MrBroccoliJP/MementoFrame/mementoframe/updater.py

#!/usr/bin/env python3
# MementoFrame - Raspberry Pi Smart Photo Frame
# Updater / installer helper

from __future__ import annotations

import argparse
import hashlib
import json
import runpy
import os
import re
import shutil
import stat
import subprocess
import sys
import tempfile
import threading
import time
import urllib.request
import zipfile
from datetime import datetime
from contextlib import contextmanager
from pathlib import Path
from typing import Any

UPDATER_BUILD = "2026-10-06-install-only-overlay-v3"

PROJECT_ROOT = Path(__file__).resolve().parent
CONFIG_FILE = PROJECT_ROOT / "config.json"
RUNTIME_DIR = PROJECT_ROOT / "runtime"
STATE_FILE = RUNTIME_DIR / "update_state.json"
STATE_LOCK_FILE = RUNTIME_DIR / "update_state.lock"
UPDATER_LOCK_FILE = RUNTIME_DIR / "updater.lock"
DOWNLOAD_DIR = RUNTIME_DIR / "update_downloads"
BACKUP_ROOT = PROJECT_ROOT.parent / "mementoframe_backups"
BACKUP_RETENTION_COUNT = 3
DEFAULT_UPDATE_TIME = "07:00"
DEFAULT_PRESERVE = ["config.json", ".env", "resources/userdata", "runtime"]
DEFAULT_SERVICES = [
    "mementoframe-config.service",
    "mementoframe-display.service",
    "mementoframe-network.service",
    "mementoframe-kiosk.service",
]
SERVICE_TEMPLATE_UNITS = [
    "mementoframe-config.service",
    "mementoframe-display.service",
    "mementoframe-network.service",
    "mementoframe-updater.service",
]
REFRESH_FROM_RELEASE_AFTER_RESTORE = ["repair_services.sh"]

REQUIRED_SYSTEMD_UNITS = [
    "mementoframe-config.service",
    "mementoframe-display.service",
    "mementoframe-network.service",
    "mementoframe-kiosk.service",
    "mementoframe-updater.service",
    "mementoframe-updater.timer",
]
REPAIR_HELPER = PROJECT_ROOT / "repair_services.sh"

HEALTH_URLS = ["http://127.0.0.1:5000/health", "http://127.0.0.1:5001/health"]
HEALTH_CHECK_ATTEMPTS = 3
HEALTH_CHECK_SECONDS = 90
HEALTH_POLL_SECONDS = 3
APP_SUBDIR = "mementoframe"

_LOCAL_STATE_LOCK = threading.RLock()

EXCLUDE_DURING_COPY = {
    ".git",
    "venv",
    "__pycache__",
    ".pytest_cache",
    "node_modules",
    "runtime",
}
SPECIAL_FILE_CLEANUP_SKIP = {
    ".git",
    "venv",
    "node_modules",
    "resources/userdata",
    "runtime",
}


def now_ts() -> int:
    return int(time.time())


def system_boot_id() -> str | None:
    """Return the Linux boot ID, which changes exactly once per reboot."""
    try:
        value = Path("/proc/sys/kernel/random/boot_id").read_text(encoding="utf-8").strip()
        return value or None
    except Exception:
        return None


def system_boot_time() -> float | None:
    """Return the Linux system boot timestamp when available."""
    try:
        for line in Path("/proc/stat").read_text(encoding="utf-8").splitlines():
            if line.startswith("btime "):
                return float(line.split()[1])
    except Exception:
        return None
    return None


def boot_changed_since_update(state: dict[str, Any], *, rollback: bool = False) -> bool:
    """Prove that the system rebooted after applying an update or rollback."""
    if rollback:
        saved_boot_id = state.get("rollback_applied_boot_id") or state.get("rollback_reboot_requested_boot_id")
        marker = state.get("rollback_reboot_requested_at") or state.get("rollback_at") or state.get("updated_at")
    else:
        saved_boot_id = state.get("update_applied_boot_id") or state.get("reboot_requested_boot_id")
        marker = state.get("reboot_requested_at") or state.get("updated_at")

    current_boot_id = system_boot_id()
    if saved_boot_id and current_boot_id:
        return saved_boot_id != current_boot_id

    boot_time = system_boot_time()
    try:
        return bool(boot_time and marker and boot_time >= float(marker))
    except (TypeError, ValueError):
        return False


@contextmanager
def interprocess_file_lock(path: Path, *, blocking: bool = True):
    """Hold a small cross-process lock file on Linux and Windows."""
    path.parent.mkdir(parents=True, exist_ok=True)
    handle = path.open("a+b")
    acquired = False
    platform_lock = None
    try:
        if os.name == "nt":
            import msvcrt

            handle.seek(0, os.SEEK_END)
            if handle.tell() == 0:
                handle.write(b"\0")
                handle.flush()
            handle.seek(0)
            mode = msvcrt.LK_LOCK if blocking else msvcrt.LK_NBLCK
            try:
                msvcrt.locking(handle.fileno(), mode, 1)
                acquired = True
                platform_lock = msvcrt
            except OSError:
                acquired = False
        else:
            import fcntl

            flags = fcntl.LOCK_EX | (0 if blocking else fcntl.LOCK_NB)
            try:
                fcntl.flock(handle.fileno(), flags)
                acquired = True
                platform_lock = fcntl
            except BlockingIOError:
                acquired = False
        yield acquired
    finally:
        if acquired and platform_lock is not None:
            try:
                if os.name == "nt":
                    handle.seek(0)
                    platform_lock.locking(handle.fileno(), platform_lock.LK_UNLCK, 1)
                else:
                    platform_lock.flock(handle.fileno(), platform_lock.LOCK_UN)
            except OSError:
                pass
        handle.close()


@contextmanager
def state_file_lock():
    """Serialize update-state read/modify/write operations across services."""
    with _LOCAL_STATE_LOCK:
        with interprocess_file_lock(STATE_LOCK_FILE) as acquired:
            if not acquired:
                raise RuntimeError("Could not lock update state")
            yield


def atomic_write_json(path: Path, data: dict[str, Any]) -> None:
    path.parent.mkdir(parents=True, exist_ok=True)
    fd, tmp_name = tempfile.mkstemp(prefix=f".{path.name}.", suffix=".tmp", dir=path.parent)
    tmp = Path(tmp_name)
    try:
        with os.fdopen(fd, "w", encoding="utf-8") as handle:
            handle.write(json.dumps(data, indent=2, sort_keys=True))
            handle.flush()
            os.fsync(handle.fileno())
        os.replace(tmp, path)
    finally:
        try:
            tmp.unlink()
        except FileNotFoundError:
            pass


def read_json(path: Path, fallback: dict[str, Any] | None = None) -> dict[str, Any]:
    fallback = fallback or {}
    try:
        return json.loads(path.read_text(encoding="utf-8"))
    except FileNotFoundError:
        return fallback.copy()
    except Exception as exc:
        return {**fallback, "_read_error": str(exc)}


def load_dotenv() -> None:
    for env_path in [PROJECT_ROOT / ".env", PROJECT_ROOT.parent / ".env"]:
        if not env_path.exists():
            continue
        try:
            for lineno, raw in enumerate(env_path.read_text(encoding="utf-8").splitlines(), 1):
                line = raw.strip()
                if not line or line.startswith("#"):
                    continue
                if "=" not in line:
                    print(f"⚠️ .env line {lineno}: ignored malformed entry: {line!r}", file=sys.stderr)
                    continue
                key, value = line.split("=", 1)
                key = key.strip()
                value = value.strip().strip('"').strip("'")
                if key and key not in os.environ:
                    os.environ[key] = value
        except Exception:
            pass


def ensure_env_file() -> bool:
    """Create a starter .env if missing. Existing files are never overwritten."""
    env_path = PROJECT_ROOT / ".env"
    if env_path.exists():
        return False
    repo_hint = os.getenv("MEMENTOFRAME_UPDATE_REPO", "MrBroccoliJP/MementoFrame")
    env_path.write_text(
        "# MementoFrame local secrets and optional update settings\n"
        "# Leave Spotify values blank to keep Spotify disconnected.\n"
        "SPOTIFY_CLIENT_ID=\n"
        "SPOTIFY_CLIENT_SECRET=\n"
        "SPOTIFY_REDIRECT_URI=https://httpbin.org/anything\n"
        "\n"
        "# Optional. Needed for private GitHub repositories or higher API limits.\n"
        "GITHUB_TOKEN=\n"
        "\n"
        "# Optional. Overrides config.json updates.repo when set.\n"
        f"MEMENTOFRAME_UPDATE_REPO={repo_hint}\n",
        encoding="utf-8",
    )
    try:
        env_path.chmod(0o600)
    except Exception:
        pass
    return True


def installed_version() -> str:
    """Read the generated composite version from version_info.py without import cache."""
    version_file = PROJECT_ROOT / "version_info.py"
    try:
        data = runpy.run_path(str(version_file))
        version = data.get("GLOBAL_APP_VERSION")
        if version:
            return str(version)
    except Exception:
        pass
    return "0.0.0.0.0.0"


def base_state(**updates: Any) -> dict[str, Any]:
    state = {
        "updater_build": UPDATER_BUILD,
        "installed_version": installed_version(),
        "latest_version": None,
        "latest_tag": None,
        "release_name": None,
        "release_notes": "",
        "release_url": None,
        "zipball_url": None,
        "available": False,
        "checked_at": None,
        "pending_restart": False,
        "reboot_requested": False,
        "download_in_progress": False,
        "update_in_progress": False,
        "update_phase": "idle",
        "applied_update": False,
        "rollback_in_progress": False,
        "rollback_reboot_requested": False,
        "last_error": None,
        "broken_releases": [],
    }
    state.update(updates)
    return state


ACTIVE_UPDATE_STATE_FIELDS = [
    "download_in_progress",
    "download_started_at",
    "update_in_progress",
    "update_phase",
    "update_session_id",
    "update_started_at",
    "update_completed_at",
    "update_failed_at",
    "update_candidate_version",
    "update_candidate_tag",
    "pending_restart",
    "reboot_requested",
    "reboot_requested_at",
    "reboot_requested_boot_id",
    "update_applied_boot_id",
    "post_reboot_pending",
    "post_reboot_waiting_for_restart",
    "post_reboot_attempt",
    "post_reboot_attempts_total",
    "post_reboot_checked_at",
    "applied_update",
    "updated_at",
    "backup_path",
    "release_root",
    "copied_top_level",
    "restored_preserved",
    "refreshed_release_files",
    "removed_special_files",
    "fixed_permissions",
    "rollback_required",
    "rollback_applied",
    "rollback_in_progress",
    "rollback_reboot_requested",
    "rollback_reboot_requested_at",
    "rollback_reboot_requested_boot_id",
    "rollback_applied_boot_id",
    "post_rollback_pending",
    "rollback_post_reboot_attempt",
    "rollback_post_reboot_attempts_total",
    "post_rollback_checked_at",
    "rollback_backup_path",
    "broken_releases",
]


ACTIVE_UPDATE_PHASES = {
    "downloading",
    "preparing",
    "applying",
    "awaiting_reboot",
    "verifying",
    "rolling_back",
    "awaiting_rollback_reboot",
    "verifying_rollback",
}


def active_update_state(state: dict[str, Any]) -> bool:
    """Return True while an update/rollback still needs its reboot flow."""
    return bool(
        state.get("download_in_progress")
        or state.get("update_in_progress")
        or state.get("pending_restart")
        or state.get("reboot_requested")
        or state.get("rollback_in_progress")
        or state.get("rollback_reboot_requested")
        or state.get("post_reboot_pending")
        or state.get("post_rollback_pending")
        or state.get("update_phase") in ACTIVE_UPDATE_PHASES
    )


def can_start_background_update(
    state: dict[str, Any],
    *,
    operation_slot_available: bool,
    current_time: float | None = None,
    startup_grace_seconds: int = 30,
) -> bool:
    """Allow a new request unless a live/non-recoverable lifecycle is active."""
    if not active_update_state(state):
        return True

    applying_only = bool(
        (
            state.get("download_in_progress")
            or state.get("update_in_progress")
            or state.get("update_phase") in {"downloading", "preparing", "applying"}
        )
        and not state.get("pending_restart")
        and not state.get("reboot_requested")
        and not state.get("rollback_in_progress")
        and not state.get("rollback_reboot_requested")
        and not state.get("post_reboot_pending")
        and not state.get("post_rollback_pending")
    )
    if not applying_only or not operation_slot_available:
        return False

    try:
        last_activity = float(state.get("state_updated_at") or state.get("update_started_at") or 0)
    except (TypeError, ValueError):
        last_activity = 0
    now = time.time() if current_time is None else current_time
    return now - last_activity >= startup_grace_seconds


def preserved_active_update_fields(previous: dict[str, Any], updates: dict[str, Any]) -> dict[str, Any]:
    """Keep unrelated state refreshes from hiding an update overlay mid-install."""
    if not active_update_state(previous):
        return {}

    preserved: dict[str, Any] = {}
    for key in ACTIVE_UPDATE_STATE_FIELDS:
        if key in updates or key not in previous:
            continue
        value = previous.get(key)
        if value in (None, False):
            continue
        preserved[key] = value
    return preserved


def replace_state(*, preserve_active_update: bool = True, **updates: Any) -> dict[str, Any]:
    with state_file_lock():
        previous = read_json(STATE_FILE, {})
        state = base_state(**updates)
        if preserve_active_update:
            state.update(preserved_active_update_fields(previous, updates))
        try:
            previous_revision = int(previous.get("state_revision") or 0)
        except (TypeError, ValueError):
            previous_revision = 0
        state["state_revision"] = previous_revision + 1
        state["state_updated_at"] = now_ts()
        atomic_write_json(STATE_FILE, state)
        return state


def write_state(**updates: Any) -> dict[str, Any]:
    with state_file_lock():
        state = read_json(STATE_FILE, {})
        try:
            previous_revision = int(state.get("state_revision") or 0)
        except (TypeError, ValueError):
            previous_revision = 0
        state.update({"updater_build": UPDATER_BUILD, "installed_version": installed_version()})
        state.update(updates)
        state["state_revision"] = previous_revision + 1
        state["state_updated_at"] = now_ts()
        state.setdefault("latest_version", None)
        state.setdefault("available", False)
        state.setdefault("pending_restart", False)
        state.setdefault("reboot_requested", False)
        state.setdefault("download_in_progress", False)
        state.setdefault("update_in_progress", False)
        state.setdefault("update_phase", "idle")
        state.setdefault("applied_update", False)
        state.setdefault("rollback_in_progress", False)
        state.setdefault("rollback_reboot_requested", False)
        state.setdefault("last_error", None)
        state.setdefault("broken_releases", [])
        atomic_write_json(STATE_FILE, state)
        return state


def load_config() -> dict[str, Any]:
    load_dotenv()
    cfg = read_json(CONFIG_FILE, {})
    cfg.setdefault("updates", {})
    updates = cfg["updates"]
    updates.setdefault("auto_update", False)
    updates.setdefault("repo", os.getenv("MEMENTOFRAME_UPDATE_REPO", "MrBroccoliJP/MementoFrame"))
    if os.getenv("MEMENTOFRAME_UPDATE_REPO"):
        updates["repo"] = os.getenv("MEMENTOFRAME_UPDATE_REPO", "")
    updates.setdefault("channel", "stable")
    updates.setdefault("preserve", DEFAULT_PRESERVE)
    updates["service_names"] = REQUIRED_SYSTEMD_UNITS
    return cfg


def save_config(cfg: dict[str, Any]) -> None:
    atomic_write_json(CONFIG_FILE, cfg)


def parse_version(v: str) -> tuple[int, ...]:
    """Parse all numeric segments of tags like v1.25.22.21.21.13."""
    parts = re.findall(r"\d+", str(v).strip().lstrip("vV"))
    return tuple(int(p) for p in parts) or (0,)


def version_newer(latest: str, current: str) -> bool:
    a = parse_version(latest)
    b = parse_version(current)
    n = max(len(a), len(b))
    return a + (0,) * (n - len(a)) > b + (0,) * (n - len(b))


def release_key(version: str | None = None, tag: str | None = None) -> str:
    """Build a stable key for release block-list comparisons."""
    value = (tag or version or "").strip()
    if not value:
        return ""
    return value.lstrip("vV")


def broken_release_keys(state: dict[str, Any]) -> set[str]:
    """Return version/tag keys for releases previously marked as broken."""
    keys: set[str] = set()
    for item in state.get("broken_releases") or []:
        if not isinstance(item, dict):
            continue
        for value in [item.get("version"), item.get("tag")]:
            key = release_key(str(value) if value else None)
            if key:
                keys.add(key)
    return keys


def release_is_marked_broken(version: str | None, tag: str | None, state: dict[str, Any]) -> bool:
    """Return True if the candidate release should not be installed again."""
    keys = broken_release_keys(state)
    return bool((version and release_key(version) in keys) or (tag and release_key(tag) in keys))


def add_broken_release(state: dict[str, Any], reason: str) -> list[dict[str, Any]]:
    """Mark the release from the current update state as broken, without duplicates."""
    version = str(state.get("latest_version") or state.get("update_candidate_version") or "").lstrip("vV")
    tag = str(state.get("latest_tag") or state.get("update_candidate_tag") or "").strip()
    url = state.get("release_url")
    key_values = {release_key(version), release_key(tag)} - {""}

    broken: list[dict[str, Any]] = []
    for item in state.get("broken_releases") or []:
        if isinstance(item, dict):
            broken.append(item)

    existing = broken_release_keys({"broken_releases": broken})
    if key_values and not (key_values & existing):
        broken.append({
            "version": version or None,
            "tag": tag or None,
            "release_url": url,
            "reason": reason,
            "marked_at": now_ts(),
        })
    return broken


def systemd_unit_exists(unit: str) -> bool:
    """Return True when systemd knows about this unit or its unit file exists."""
    if (Path("/etc/systemd/system") / unit).exists():
        return True
    try:
        proc = subprocess.run(
            ["systemctl", "list-unit-files", unit],
            text=True,
            capture_output=True,
            timeout=10,
        )
        return proc.returncode == 0 and unit in proc.stdout
    except Exception:
        return False


def systemd_unit_state(unit: str) -> dict[str, Any]:
    """Return a small systemd status record for one expected unit."""
    exists = systemd_unit_exists(unit)
    out: dict[str, Any] = {"exists": exists, "enabled": None, "active": None}
    if not exists:
        return out

    for key, cmd in {
        "enabled": ["systemctl", "is-enabled", unit],
        "active": ["systemctl", "is-active", unit],
    }.items():
        try:
            proc = subprocess.run(cmd, text=True, capture_output=True, timeout=10)
            out[key] = (proc.stdout.strip() or proc.stderr.strip() or "unknown")
        except Exception as exc:
            out[key] = f"unknown: {exc}"
    return out


def systemd_compatibility_state() -> dict[str, Any]:
    """Return whether this install has all expected MementoFrame systemd units."""
    units = {unit: systemd_unit_state(unit) for unit in REQUIRED_SYSTEMD_UNITS}
    missing = [unit for unit, info in units.items() if not info.get("exists")]
    stale = systemd_units_needing_template_refresh()
    helper_stale = repair_helper_needs_template_refresh()
    return {
        "required_units": REQUIRED_SYSTEMD_UNITS,
        "units": units,
        "missing_units": missing,
        "stale_template_units": stale,
        "compatible": not missing and not stale,
        "repair_helper": str(REPAIR_HELPER),
        "repair_helper_exists": REPAIR_HELPER.exists(),
        "repair_helper_stale": helper_stale,
    }


def repair_helper_needs_template_refresh() -> bool:
    """Return True when the installed root repair helper still has old unit templates."""
    try:
        text = REPAIR_HELPER.read_text(encoding="utf-8", errors="replace")
    except FileNotFoundError:
        return False
    except Exception:
        return False
    return "network-online.target" in text


def systemd_units_needing_template_refresh() -> list[str]:
    """
    Return installed units whose template has known obsolete boot ordering.

    Older MementoFrame units waited for network-online.target. That prevents the
    network watchdog from creating AP mode when Wi-Fi is unavailable at boot.
    """
    stale: list[str] = []
    for unit in SERVICE_TEMPLATE_UNITS:
        unit_path = Path("/etc/systemd/system") / unit
        try:
            text = unit_path.read_text(encoding="utf-8", errors="replace")
        except FileNotFoundError:
            continue
        except Exception:
            continue
        if "network-online.target" in text:
            stale.append(unit)
    return stale


def repair_systemd_services_if_needed() -> dict[str, Any]:
    """Repair missing or stale MementoFrame systemd units through the root helper."""
    before = systemd_compatibility_state()
    if not before["missing_units"] and not before["stale_template_units"]:
        state = write_state(
            systemd_compatible=True,
            missing_systemd_units=[],
            stale_systemd_units=[],
            repair_helper_stale=before["repair_helper_stale"],
            service_repair_needed=False,
            service_repair_attempted=False,
            service_repair_error=None,
        )
        return {"ok": True, "changed": False, "before": before, "after": before, "state": state}

    if not REPAIR_HELPER.exists():
        msg = f"Missing required systemd units and repair helper is not installed: {REPAIR_HELPER}"
        state = write_state(
            systemd_compatible=False,
            missing_systemd_units=before["missing_units"],
            stale_systemd_units=before["stale_template_units"],
            service_repair_needed=True,
            service_repair_attempted=False,
            service_repair_error=msg,
            last_error=msg,
        )
        return {"ok": False, "changed": False, "before": before, "after": before, "error": msg, "state": state}

    if before["repair_helper_stale"]:
        msg = (
            "Systemd units need repair, but repair_services.sh is still the preserved old helper. "
            "Refresh repair_services.sh from the current release or rerun the installer once, then run repair-services."
        )
        state = write_state(
            systemd_compatible=False,
            missing_systemd_units=before["missing_units"],
            stale_systemd_units=before["stale_template_units"],
            repair_helper_stale=True,
            service_repair_needed=True,
            service_repair_attempted=False,
            service_repair_error=msg,
            last_error=msg,
        )
        return {"ok": False, "changed": False, "before": before, "after": before, "error": msg, "state": state}

    proc = sudo_cmd(str(REPAIR_HELPER), timeout=60)
    after = systemd_compatibility_state()
    ok = proc.returncode == 0 and not after["missing_units"] and not after["stale_template_units"]
    msg = "" if ok else (proc.stderr.strip() or proc.stdout.strip() or f"repair helper exited with {proc.returncode}")

    state = write_state(
        systemd_compatible=ok,
        missing_systemd_units=after["missing_units"],
        stale_systemd_units=after["stale_template_units"],
        service_repair_needed=bool(after["missing_units"] or after["stale_template_units"]),
        service_repair_attempted=True,
        service_repair_at=now_ts(),
        service_repair_stdout=proc.stdout.strip(),
        service_repair_stderr=proc.stderr.strip(),
        service_repair_error=None if ok else msg,
        last_error=None if ok else msg,
    )
    return {"ok": ok, "changed": True, "before": before, "after": after, "error": None if ok else msg, "state": state}


def http_json(url: str, timeout: int = 15) -> Any:
    headers = {"Accept": "application/vnd.github+json", "User-Agent": "MementoFrame-Updater"}
    token = os.getenv("GITHUB_TOKEN", "").strip()
    if token:
        headers["Authorization"] = f"Bearer {token}"
    req = urllib.request.Request(url, headers=headers)
    with urllib.request.urlopen(req, timeout=timeout) as res:
        return json.loads(res.read().decode("utf-8"))


def github_latest_release(repo: str, channel: str = "stable") -> dict[str, Any]:
    if not repo or "/" not in repo:
        raise RuntimeError("Update repo is not configured. Set updates.repo or MEMENTOFRAME_UPDATE_REPO.")
    if channel in {"pre-release", "prerelease", "pre_release"}:
        releases = http_json(f"https://api.github.com/repos/{repo}/releases?per_page=30")
        if not isinstance(releases, list) or not releases:
            raise RuntimeError("No GitHub releases found.")
        candidates = [r for r in releases if not r.get("draft") and r.get("tag_name")]
        if not candidates:
            raise RuntimeError("No non-draft releases found.")
        return max(candidates, key=lambda r: parse_version(str(r.get("tag_name") or "")))
    return http_json(f"https://api.github.com/repos/{repo}/releases/latest")


def reusable_download_fields(previous_state: dict[str, Any], zipball_url: str | None) -> dict[str, Any]:
    """Carry staged download metadata forward when a check sees the same release."""
    if not zipball_url:
        return {}

    downloaded_url = previous_state.get("downloaded_zipball_url")
    downloaded_archive = previous_state.get("downloaded_archive")
    if downloaded_url != zipball_url or not downloaded_archive:
        return {}

    archive = Path(str(downloaded_archive))
    if not archive.exists() or not archive.is_file():
        return {}

    fields: dict[str, Any] = {
        "download_ready": True,
        "downloaded_archive": str(archive),
        "downloaded_zipball_url": zipball_url,
    }
    for key in ["downloaded_at", "downloaded_sha256"]:
        if previous_state.get(key):
            fields[key] = previous_state[key]
    return fields


def check_for_update(*, stage_download: bool = True) -> dict[str, Any]:
    cfg = load_config()
    updates = cfg.get("updates", {})
    repo = updates.get("repo", "")
    channel = updates.get("channel", "stable")
    current = installed_version()
    previous_state = read_json(STATE_FILE, {})
    broken_releases = previous_state.get("broken_releases") or []
    try:
        release = github_latest_release(repo, channel=channel)
        latest = str(release.get("tag_name") or "").lstrip("v")
        tag = release.get("tag_name")
        is_broken = release_is_marked_broken(latest, str(tag) if tag else None, previous_state)
        available = bool(latest and version_newer(latest, current) and not is_broken)
        zipball_url = release.get("zipball_url")
        download_fields = reusable_download_fields(previous_state, zipball_url)

        common = dict(
            installed_version=current,
            latest_version=latest or None,
            latest_tag=tag,
            release_name=release.get("name"),
            release_notes=release.get("body") or "",
            release_url=release.get("html_url"),
            zipball_url=zipball_url,
            release_assets=release.get("assets") or [],
            checked_at=now_ts(),
            broken_releases=broken_releases,
            **download_fields,
        )

        if is_broken:
            return replace_state(
                **common,
                available=False,
                broken_release_skipped=True,
                last_error=f"Latest release {tag or latest} is marked as broken after a failed update; waiting for a newer release.",
            )

        state = replace_state(
            **common,
            available=available,
            broken_release_skipped=False,
            last_error=None,
        )
        if available and stage_download:
            state = stage_release_download(state)
        return state
    except Exception as exc:
        return replace_state(
            installed_version=current,
            checked_at=now_ts(),
            available=False,
            broken_releases=broken_releases,
            last_error=str(exc),
        )


def prepare_reinstall_current_release() -> dict[str, Any]:
    """
    Prepare the configured channel's latest release for a forced reinstall.

    This intentionally marks the candidate available even when its version is
    equal to the installed version. If a release archive is already staged, use
    that local archive before attempting any network request.
    """
    previous_state = read_json(STATE_FILE, {})
    cached = cached_archive_for_state(previous_state)
    if cached and previous_state.get("zipball_url"):
        return write_state(
            available=True,
            force_reinstall=True,
            reinstall_requested_at=now_ts(),
            download_ready=True,
            downloaded_archive=str(cached),
            last_error=None,
        )

    cfg = load_config()
    updates = cfg.get("updates", {})
    repo = updates.get("repo", "")
    channel = updates.get("channel", "stable")
    current = installed_version()
    release = github_latest_release(repo, channel=channel)
    latest = str(release.get("tag_name") or "").lstrip("v")
    tag = release.get("tag_name")
    zipball_url = release.get("zipball_url")
    download_fields = reusable_download_fields(previous_state, zipball_url)

    if release_is_marked_broken(latest, str(tag) if tag else None, previous_state):
        return replace_state(
            installed_version=current,
            latest_version=latest or None,
            latest_tag=tag,
            available=False,
            update_in_progress=bool(previous_state.get("update_in_progress")),
            checked_at=now_ts(),
            last_error=f"Release {tag or latest} is marked as broken after a failed update; reinstall skipped.",
        )

    state = replace_state(
        installed_version=current,
        latest_version=latest or None,
        latest_tag=tag,
        release_name=release.get("name"),
        release_notes=release.get("body") or "",
        release_url=release.get("html_url"),
        zipball_url=zipball_url,
        release_assets=release.get("assets") or [],
        checked_at=now_ts(),
        available=True,
        force_reinstall=True,
        reinstall_requested_at=now_ts(),
        update_in_progress=bool(previous_state.get("update_in_progress")),
        update_phase="applying" if previous_state.get("update_in_progress") else previous_state.get("update_phase", "idle"),
        update_started_at=previous_state.get("update_started_at") or now_ts(),
        **download_fields,
        last_error=None,
    )
    return stage_release_download(state)


def release_archive_name(state: dict[str, Any]) -> str:
    """Return a filesystem-safe archive filename for the candidate release."""
    raw = str(state.get("latest_tag") or state.get("latest_version") or "candidate")
    clean = re.sub(r"[^A-Za-z0-9_.-]+", "-", raw).strip(".-") or "candidate"
    return f"{clean}.zip"


def cached_archive_for_state(state: dict[str, Any]) -> Path | None:
    """Return the staged archive path when it matches the current candidate."""
    path_value = state.get("downloaded_archive")
    if not path_value:
        return None
    path = Path(str(path_value))
    if not path.exists() or not path.is_file():
        return None
    if state.get("downloaded_zipball_url") != state.get("zipball_url"):
        return None
    return path


def stage_release_download(state: dict[str, Any]) -> dict[str, Any]:
    """
    Download the candidate archive as soon as an update is discovered.

    This lets the install window use a cached zip if Wi-Fi is unavailable later.
    """
    zipball_url = state.get("zipball_url")
    if not zipball_url:
        return state

    cached = cached_archive_for_state(state)
    if cached:
        return write_state(
            download_ready=True,
            downloaded_archive=str(cached),
            downloaded_zipball_url=zipball_url,
            last_error=None,
        )

    DOWNLOAD_DIR.mkdir(parents=True, exist_ok=True)
    dest = DOWNLOAD_DIR / release_archive_name(state)
    tmp = dest.with_suffix(dest.suffix + ".tmp")
    release_assets: list[dict[str, Any]] = state.get("release_assets") or []
    expected_sha256 = fetch_release_checksum(release_assets, "release.zip")
    sha256 = download_file(str(zipball_url), tmp, expected_sha256=expected_sha256)
    os.replace(tmp, dest)
    return write_state(
        download_ready=True,
        downloaded_archive=str(dest),
        downloaded_zipball_url=zipball_url,
        downloaded_at=now_ts(),
        downloaded_sha256=sha256,
        last_error=None,
    )

def should_preserve(rel: str, preserve: list[str]) -> bool:
    rel = rel.strip("/")
    return any(rel == p.strip("/") or rel.startswith(p.strip("/") + "/") for p in preserve if p.strip("/"))


def is_excluded(rel: str) -> bool:
    rel = rel.strip("/")
    return any(rel == p or rel.startswith(p + "/") for p in EXCLUDE_DURING_COPY)


def is_special_file(path: Path) -> bool:
    try:
        mode = os.lstat(path).st_mode
    except OSError:
        return True
    return not (stat.S_ISDIR(mode) or stat.S_ISREG(mode) or stat.S_ISLNK(mode))


def cleanup_special_files(root: Path = PROJECT_ROOT) -> list[str]:
    removed: list[str] = []
    for dirpath, dirnames, filenames in os.walk(root):
        current = Path(dirpath)
        try:
            rel_dir = str(current.relative_to(root)).strip(".")
        except Exception:
            rel_dir = ""
        keep_dirs = []
        for d in dirnames:
            rel = f"{rel_dir}/{d}".strip("/") if rel_dir else d
            if any(rel == skip or rel.startswith(skip + "/") for skip in SPECIAL_FILE_CLEANUP_SKIP):
                continue
            keep_dirs.append(d)
        dirnames[:] = keep_dirs
        for name in filenames:
            path = current / name
            try:
                if is_special_file(path):
                    rel = str(path.relative_to(root))
                    path.unlink()
                    removed.append(rel)
            except Exception as exc:
                removed.append(f"{path}: failed to remove ({exc})")
    return removed


def copy_one(src: Path, dst: Path, rel: str, preserve: list[str], copied_top: set[str]) -> None:
    rel = rel.strip("/")
    if not rel or should_preserve(rel, preserve) or is_excluded(rel):
        return
    if is_special_file(src):
        return
    top = rel.split("/", 1)[0]
    copied_top.add(top)
    if src.is_dir() and not src.is_symlink():
        dst.mkdir(parents=True, exist_ok=True)
        for child in src.iterdir():
            copy_one(child, dst / child.name, f"{rel}/{child.name}", preserve, copied_top)
        return
    dst.parent.mkdir(parents=True, exist_ok=True)
    if dst.exists() and dst.is_dir():
        shutil.rmtree(dst)
    shutil.copy2(src, dst, follow_symlinks=False)


def copy_tree_contents(src: Path, dst: Path, preserve: list[str]) -> list[str]:
    copied_top: set[str] = set()
    for item in src.iterdir():
        copy_one(item, dst / item.name, item.name, preserve, copied_top)
    return sorted(copied_top)


def backup_ignore(directory: str, names: list[str], preserve: list[str] | None = None) -> set[str]:
    ignored = set(shutil.ignore_patterns(
        "venv", "__pycache__", ".git", ".pytest_cache", "node_modules",
    )(directory, names))
    preserve = preserve or []
    for name in names:
        if name in ignored:
            continue
        path = Path(directory) / name
        try:
            rel = path.resolve().relative_to(PROJECT_ROOT.resolve()).as_posix()
        except ValueError:
            rel = ""
        # Preserved data remains live throughout both update and rollback, so
        # copying it into the code backup only wastes time and risks restoring
        # stale runtime state later.
        if rel and should_preserve(rel, preserve):
            ignored.add(name)
            continue
        if is_special_file(path):
            ignored.add(name)
    return ignored


def backup_current(preserve: list[str] | None = None) -> Path:
    cleanup_special_files(PROJECT_ROOT)
    BACKUP_ROOT.mkdir(parents=True, exist_ok=True)
    stamp = datetime.now().strftime("%Y%m%d-%H%M%S")
    dest = BACKUP_ROOT / f"mementoframe-{installed_version()}-{stamp}"
    shutil.copytree(
        PROJECT_ROOT,
        dest,
        ignore=lambda directory, names: backup_ignore(directory, names, preserve),
        ignore_dangling_symlinks=True,
    )
    return dest


def list_backup_dirs() -> list[Path]:
    """Return MementoFrame backup directories, newest first."""
    if not BACKUP_ROOT.exists():
        return []

    backups: list[Path] = []
    for path in BACKUP_ROOT.iterdir():
        if path.is_dir() and path.name.startswith("mementoframe-"):
            backups.append(path)

    return sorted(backups, key=lambda p: p.stat().st_mtime, reverse=True)


def prune_old_backups(keep: int = BACKUP_RETENTION_COUNT) -> dict[str, Any]:
    """Delete old update backups, keeping the newest `keep` directories.

    This should only run after a successful post-update health check. The most
    recent backups are kept so rollback remains possible for current and recent
    updates, while old backups do not accumulate forever.
    """
    keep = max(0, int(keep))
    backups = list_backup_dirs()
    kept = backups[:keep]
    candidates = backups[keep:]

    deleted: list[str] = []
    failed: list[dict[str, str]] = []

    for backup in candidates:
        try:
            shutil.rmtree(backup)
            deleted.append(str(backup))
        except Exception as exc:
            failed.append({"path": str(backup), "error": str(exc)})

    return {
        "backup_retention_count": keep,
        "backup_root": str(BACKUP_ROOT),
        "backups_kept": [str(p) for p in kept],
        "backups_deleted": deleted,
        "backup_prune_failed": failed,
    }


def find_release_app_root(extract_dir: Path) -> Path:
    candidates: list[Path] = []
    for root, _dirs, files in os.walk(extract_dir):
        p = Path(root)
        if "config_portal_service.py" in files and "display_service.py" in files:
            candidates.append(p)
    if not candidates:
        raise RuntimeError("Could not find config_portal_service.py + display_service.py inside release archive.")
    for candidate in candidates:
        if candidate.name == APP_SUBDIR:
            return candidate
    return sorted(candidates, key=lambda p: len(p.parts))[0]


def run(cmd: list[str], check: bool = False, timeout: int | None = None) -> subprocess.CompletedProcess[str]:
    proc = subprocess.run(cmd, cwd=PROJECT_ROOT, text=True, capture_output=True, timeout=timeout)
    if check and proc.returncode != 0:
        raise RuntimeError(f"Command failed: {' '.join(cmd)}\n{proc.stderr or proc.stdout}")
    return proc


def sudo_cmd(*cmd: str, timeout: int = 30) -> subprocess.CompletedProcess[str]:
    return run(["sudo", "-n", *cmd], check=False, timeout=timeout)


def restart_services(services: list[str]) -> None:
    for svc in services:
        proc = sudo_cmd("systemctl", "restart", svc, timeout=30)
        if proc.returncode != 0:
            print(f"⚠️ systemctl restart {svc}: {proc.stderr.strip() or proc.stdout.strip()}")


def download_file(url: str, dest: Path, timeout: int = 60, expected_sha256: str | None = None) -> str:
    headers = {"User-Agent": "MementoFrame-Updater"}
    token = os.getenv("GITHUB_TOKEN", "").strip()
    if token:
        headers["Authorization"] = f"Bearer {token}"
    req = urllib.request.Request(url, headers=headers)
    h = hashlib.sha256()
    with urllib.request.urlopen(req, timeout=timeout) as res, dest.open("wb") as f:
        while True:
            chunk = res.read(1024 * 256)
            if not chunk:
                break
            h.update(chunk)
            f.write(chunk)
    digest = h.hexdigest()
    if expected_sha256 and digest != expected_sha256.lower():
        dest.unlink(missing_ok=True)
        raise RuntimeError(f"SHA-256 mismatch: expected {expected_sha256.lower()!r}, got {digest!r}")
    return digest


def file_sha256(path: Path) -> str:
    """Return the SHA-256 digest of an existing local file."""
    h = hashlib.sha256()
    with path.open("rb") as f:
        while True:
            chunk = f.read(1024 * 256)
            if not chunk:
                break
            h.update(chunk)
    return h.hexdigest()


def fetch_release_checksum(release_assets: list[dict[str, Any]], filename: str) -> str | None:
    for asset in release_assets:
        name = str(asset.get("name") or "").lower()
        if name in {"checksums.txt", "sha256sums.txt", "checksums.sha256"}:
            url = asset.get("browser_download_url") or asset.get("url")
            if not url:
                continue
            try:
                headers = {"User-Agent": "MementoFrame-Updater"}
                token = os.getenv("GITHUB_TOKEN", "").strip()
                if token:
                    headers["Authorization"] = f"Bearer {token}"
                req = urllib.request.Request(url, headers=headers)
                with urllib.request.urlopen(req, timeout=15) as res:
                    text = res.read().decode("utf-8", errors="replace")
                for line in text.splitlines():
                    parts = line.split()
                    if len(parts) == 2 and parts[1].lstrip("*") == filename:
                        return parts[0].lower()
            except Exception:
                pass
    return None


def repair_runtime_permissions() -> list[str]:
    fixed: list[str] = []
    for rel in ["updater.py", "network_manager_service.py", "config_portal_service.py", "display_service.py"]:
        path = PROJECT_ROOT / rel
        if not path.exists():
            continue
        try:
            path.chmod(path.stat().st_mode | 0o755)
            fixed.append(rel)
        except Exception as exc:
            fixed.append(f"{rel}: failed to chmod ({exc})")
    return fixed


def refresh_release_managed_files(release_root: Path) -> list[str]:
    """
    Copy updater-managed helper files from the release after preserved files are restored.

    Some older installs preserved repair_services.sh. Refreshing it explicitly lets
    service-template fixes roll out through the updater itself.
    """
    refreshed: list[str] = []
    for rel in REFRESH_FROM_RELEASE_AFTER_RESTORE:
        src = release_root / rel
        dest = PROJECT_ROOT / rel
        if not src.exists():
            continue
        try:
            dest.parent.mkdir(parents=True, exist_ok=True)
            shutil.copy2(src, dest)
            dest.chmod(dest.stat().st_mode | 0o755)
        except Exception as exc:
            refreshed.append(f"{rel}: refresh failed ({exc})")
        else:
            refreshed.append(rel)
    return refreshed


def install_requirements() -> None:
    req = PROJECT_ROOT / "requirements.txt"
    if not req.exists():
        return
    pip = PROJECT_ROOT / "venv" / "bin" / "pip"
    if pip.exists():
        run([str(pip), "install", "-r", str(req)], check=True, timeout=600)
    else:
        run([sys.executable, "-m", "pip", "install", "-r", str(req)], check=True, timeout=600)


def apply_update(allow_reinstall: bool = False) -> dict[str, Any]:
    cfg = load_config()
    preserve = list(cfg.get("updates", {}).get("preserve") or DEFAULT_PRESERVE)
    state = read_json(STATE_FILE, {})
    if state.get("pending_restart") or state.get("reboot_requested"):
        return state

    # Track release discovery, download, and preparation without activating the
    # display overlay. update_in_progress is latched only immediately before we
    # begin changing the installed application files below.
    state = write_state(
        download_in_progress=True,
        update_in_progress=False,
        update_phase="downloading",
        update_session_id=state.get("update_session_id") or f"{now_ts()}-{os.getpid()}",
        download_started_at=state.get("download_started_at") or now_ts(),
        update_started_at=None,
        update_completed_at=None,
        update_failed_at=None,
        pending_restart=False,
        reboot_requested=False,
        reboot_requested_at=None,
        reboot_requested_boot_id=None,
        update_applied_boot_id=None,
        applied_update=False,
        post_reboot_pending=False,
        post_reboot_waiting_for_restart=False,
        post_reboot_attempt=None,
        post_reboot_attempts_total=None,
        post_reboot_checked_at=None,
        rollback_required=False,
        rollback_applied=False,
        rollback_in_progress=False,
        rollback_reboot_requested=False,
        rollback_reboot_requested_at=None,
        rollback_reboot_requested_boot_id=None,
        rollback_applied_boot_id=None,
        post_rollback_pending=False,
        rollback_post_reboot_attempt=None,
        rollback_post_reboot_attempts_total=None,
        post_rollback_checked_at=None,
        last_error=None,
    )
    backup: Path | None = None
    sha256 = ""
    release_root_str = None
    copied: list[str] = []
    restored_preserved: list[str] = []
    fixed_permissions: list[str] = []
    removed_special_files: list[str] = []
    refreshed_release_files: list[str] = []
    service_repair: dict[str, Any] | None = None

    try:
        has_reinstall_archive = allow_reinstall and bool(cached_archive_for_state(state))
        if not has_reinstall_archive and (not state.get("zipball_url") or not state.get("available")):
            state = check_for_update(stage_download=False)
        if has_reinstall_archive:
            state = write_state(available=True, force_reinstall=True, last_error=None)
        if not state.get("available") and not allow_reinstall:
            return write_state(
                download_in_progress=False,
                update_in_progress=False,
                update_phase="idle",
                update_completed_at=now_ts(),
                applied_update=False,
            )
        if not state.get("zipball_url"):
            raise RuntimeError("No release archive URL is available for update installation.")

        latest = state.get("latest_version") or state.get("latest_tag") or "unknown"
        state = write_state(
            download_in_progress=True,
            update_in_progress=False,
            update_phase="downloading",
            update_candidate_version=str(state.get("latest_version") or "").lstrip("vV") or None,
            update_candidate_tag=state.get("latest_tag"),
            last_error=None,
        )
        state = stage_release_download(state)
        cached_archive = cached_archive_for_state(state)
        if not cached_archive:
            raise RuntimeError("The release archive was not staged successfully.")

        with tempfile.TemporaryDirectory(prefix="mementoframe-update-") as td:
            tmp = Path(td)
            archive = tmp / "release.zip"
            state = write_state(update_phase="preparing")
            shutil.copy2(cached_archive, archive)
            sha256 = state.get("downloaded_sha256") or file_sha256(archive)
            extract_dir = tmp / "extract"
            extract_dir.mkdir()
            with zipfile.ZipFile(archive) as zf:
                bad = zf.testzip()
                if bad:
                    raise RuntimeError(f"Corrupted zip file: {bad}")
                zf.extractall(extract_dir)

            release_root = find_release_app_root(extract_dir)
            release_root_str = str(release_root)

            # Everything needed for the update is now local and validated.
            # From this write onward the overlay remains visible through the
            # reboot and post-reboot health verification lifecycle.
            state = write_state(
                download_in_progress=False,
                update_in_progress=True,
                update_phase="applying",
                update_started_at=now_ts(),
                update_candidate_version=str(state.get("latest_version") or "").lstrip("vV") or None,
                update_candidate_tag=state.get("latest_tag"),
                last_error=None,
            )
            removed_special_files = cleanup_special_files(PROJECT_ROOT)
            backup = backup_current(preserve)
            copied = copy_tree_contents(release_root, PROJECT_ROOT, preserve)
            refreshed_release_files = refresh_release_managed_files(release_root)
            fixed_permissions = repair_runtime_permissions()
            install_requirements()
            service_repair = repair_systemd_services_if_needed()

        service_repair_ok = service_repair is None or service_repair.get("ok")

        return write_state(
            installed_version=installed_version(),
            latest_version=str(latest).lstrip("v"),
            available=False,
            download_in_progress=False,
            update_in_progress=True,
            update_phase="awaiting_reboot",
            pending_restart=True,
            reboot_requested=False,
            update_applied_boot_id=system_boot_id(),
            applied_update=True,
            updated_at=now_ts(),
            downloaded_sha256=sha256,
            backup_path=str(backup) if backup else None,
            release_root=release_root_str,
            copied_top_level=copied,
            restored_preserved=restored_preserved,
            refreshed_release_files=refreshed_release_files,
            removed_special_files=removed_special_files,
            fixed_permissions=fixed_permissions,
            service_repair=service_repair,
            last_error=None if service_repair_ok else "Update applied, but systemd service repair failed.",
        )
    except Exception as exc:
        write_state(
            download_in_progress=False,
            update_in_progress=False,
            update_phase="failed",
            update_failed_at=now_ts(),
            last_error=str(exc),
        )
        raise


def request_reboot() -> dict[str, Any]:
    state = write_state(
        download_in_progress=False,
        update_in_progress=True,
        update_phase="awaiting_reboot",
        pending_restart=True,
        reboot_requested=True,
        reboot_requested_at=now_ts(),
        reboot_requested_boot_id=system_boot_id(),
        reboot_failed_at=None,
    )
    proc = sudo_cmd("reboot", timeout=10)
    if proc.returncode != 0:
        message = proc.stderr.strip() or proc.stdout.strip() or f"reboot exited with {proc.returncode}"
        state = write_state(
            update_in_progress=True,
            update_phase="awaiting_reboot",
            pending_restart=True,
            reboot_requested=True,
            reboot_failed_at=now_ts(),
            last_error=f"Update installed, but reboot failed: {message}",
        )
        print(f"WARNING: reboot failed: {message}")
    return state


def parse_hm(value: str) -> tuple[int, int]:
    m = re.match(r"^(\d{1,2}):(\d{2})$", str(value or ""))
    if not m:
        return (5, 0)
    return max(0, min(23, int(m.group(1)))), max(0, min(59, int(m.group(2))))


def current_minutes() -> int:
    n = datetime.now()
    return n.hour * 60 + n.minute


def auto_update_target_minute(cfg: dict[str, Any]) -> int:
    """Return the minute of day when automatic installs may happen."""
    ap = cfg.get("auto_power") or {}
    if ap.get("enabled"):
        h, m = parse_hm(ap.get("on_time", DEFAULT_UPDATE_TIME))
        return h * 60 + m
    h, m = parse_hm(DEFAULT_UPDATE_TIME)
    return h * 60 + m


def in_auto_update_window(cfg: dict[str, Any], window_minutes: int = 60) -> bool:
    target = auto_update_target_minute(cfg)
    now = current_minutes()
    return 0 <= ((now - target) % (24 * 60)) < window_minutes


def autoupdate(no_reboot: bool = False) -> dict[str, Any]:
    """Run updater startup workflow, then hourly auto-update behavior.

    Every time the updater service starts it first validates any pending reboot.
    Once that lifecycle is complete it repairs systemd units and continues with
    normal auto-update behavior.
    """
    current_state = read_json(STATE_FILE, {})
    if current_state.get("rollback_reboot_requested"):
        rollback_check = post_rollback_check()
        if rollback_check.get("rollback_in_progress") or rollback_check.get("rollback_required"):
            return rollback_check
        # Rollback is verified, so continue with normal updater behavior below.

    current_state = read_json(STATE_FILE, {})
    if current_state.get("pending_restart") or current_state.get("reboot_requested"):
        check_result = post_reboot_check()
        if check_result.get("pending_restart") or check_result.get("reboot_requested") or check_result.get("rollback_applied"):
            return check_result
        # Health is OK, so continue with normal check/update behavior below.

    current_state = read_json(STATE_FILE, {})
    if (
        current_state.get("download_in_progress")
        or current_state.get("update_in_progress")
        or current_state.get("update_phase") in {"downloading", "preparing", "applying"}
    ):
        if can_start_background_update(current_state, operation_slot_available=True):
            write_state(
                download_in_progress=False,
                update_in_progress=False,
                update_phase="interrupted",
                update_interrupted_at=now_ts(),
                last_error="Previous update process stopped before requesting a reboot; retrying safely.",
            )
        else:
            return write_state(auto_update_skipped="update_in_progress", last_autoupdate_check=now_ts())

    repair = repair_systemd_services_if_needed()
    if not repair.get("ok"):
        return write_state(auto_update_skipped="service_repair_failed", last_autoupdate_check=now_ts())

    cfg = load_config()
    if not cfg.get("updates", {}).get("auto_update"):
        return write_state(auto_update_skipped="disabled", last_autoupdate_check=now_ts())

    install_window = in_auto_update_window(cfg)
    target_minute = auto_update_target_minute(cfg)
    cached_state = read_json(STATE_FILE, {})

    if install_window and cached_state.get("available") and cached_archive_for_state(cached_state):
        state = cached_state
    else:
        # Downloads are intentionally silent. apply_update() activates the
        # overlay only after the archive is local, validated, and extracted.
        state = check_for_update(stage_download=not install_window)

    state = write_state(
        auto_update_skipped=None,
        auto_update_install_window=install_window,
        auto_update_install_target=f"{target_minute // 60:02d}:{target_minute % 60:02d}",
        last_autoupdate_check=now_ts(),
    )

    if not install_window:
        return write_state(auto_update_skipped="outside_install_window", last_autoupdate_check=now_ts())

    if state.get("available"):
        result = apply_update()
        if result.get("applied_update") and not no_reboot:
            request_reboot()
        return result

    return state

def url_ok(url: str, timeout: int = 8) -> bool:
    try:
        with urllib.request.urlopen(url, timeout=timeout) as res:
            return 200 <= int(res.status) < 300
    except Exception:
        return False


def restore_backup_after_failed_update(state: dict[str, Any], reason: str) -> dict[str, Any]:
    """Restore the previous app files and mark the failed release as broken."""
    write_state(
        update_phase="rolling_back",
        post_reboot_pending=False,
        post_reboot_waiting_for_restart=False,
        rollback_in_progress=True,
        rollback_required=True,
        rollback_started_at=now_ts(),
        last_error=f"{reason}; restoring previous version.",
    )
    backup_value = str(state.get("backup_path") or "").strip()
    broken_releases = add_broken_release(state, reason)

    if not backup_value:
        return write_state(
            broken_releases=broken_releases,
            download_in_progress=False,
            rollback_required=True,
            rollback_applied=False,
            rollback_in_progress=False,
            rollback_reboot_requested=False,
            update_in_progress=False,
            update_phase="failed",
            update_failed_at=now_ts(),
            pending_restart=False,
            reboot_requested=False,
            last_error=f"{reason}; rollback failed because no backup_path was recorded.",
        )

    backup = Path(backup_value)
    if not backup.exists() or not backup.is_dir():
        return write_state(
            broken_releases=broken_releases,
            download_in_progress=False,
            rollback_required=True,
            rollback_applied=False,
            rollback_in_progress=False,
            rollback_reboot_requested=False,
            update_in_progress=False,
            update_phase="failed",
            update_failed_at=now_ts(),
            pending_restart=False,
            reboot_requested=False,
            last_error=f"{reason}; rollback failed because backup path does not exist: {backup}",
        )

    cfg = load_config()
    preserve = list(cfg.get("updates", {}).get("preserve") or DEFAULT_PRESERVE)

    try:
        copied = copy_tree_contents(backup, PROJECT_ROOT, preserve)
        fixed_permissions = repair_runtime_permissions()
        try:
            install_requirements()
        except Exception as req_exc:
            requirement_error = str(req_exc)
        else:
            requirement_error = None

        return write_state(
            installed_version=installed_version(),
            available=False,
            download_in_progress=False,
            update_in_progress=True,
            update_phase="awaiting_rollback_reboot",
            pending_restart=True,
            reboot_requested=False,
            rollback_applied_boot_id=system_boot_id(),
            applied_update=False,
            rollback_required=False,
            rollback_applied=True,
            rollback_in_progress=True,
            rollback_reboot_requested=False,
            rollback_at=now_ts(),
            rollback_backup_path=str(backup),
            rollback_restored_top_level=copied,
            rollback_fixed_permissions=fixed_permissions,
            rollback_requirement_error=requirement_error,
            broken_releases=broken_releases,
            last_error=f"{reason}; rolled back to backup and marked release as broken.",
        )
    except Exception as exc:
        return write_state(
            broken_releases=broken_releases,
            download_in_progress=False,
            rollback_required=True,
            rollback_applied=False,
            rollback_in_progress=False,
            rollback_reboot_requested=False,
            update_in_progress=False,
            update_phase="failed",
            update_failed_at=now_ts(),
            pending_restart=False,
            reboot_requested=False,
            last_error=f"{reason}; rollback failed: {exc}",
        )


def post_reboot_check() -> dict[str, Any]:
    state = read_json(STATE_FILE, {})
    if not state.get("pending_restart") and not state.get("reboot_requested"):
        return write_state(post_reboot_checked_at=now_ts())

    if not boot_changed_since_update(state):
        return write_state(
            update_in_progress=True,
            update_phase="awaiting_reboot",
            pending_restart=True,
            post_reboot_pending=False,
            post_reboot_waiting_for_restart=True,
        )

    last_failed_urls: list[str] = []
    for attempt in range(1, HEALTH_CHECK_ATTEMPTS + 1):
        write_state(
            update_in_progress=True,
            update_phase="verifying",
            post_reboot_pending=True,
            post_reboot_waiting_for_restart=False,
            post_reboot_attempt=attempt,
            post_reboot_attempts_total=HEALTH_CHECK_ATTEMPTS,
            post_reboot_checked_at=now_ts(),
            last_error=None if attempt == 1 else "Post-reboot health check is still waiting for services.",
        )

        deadline = time.time() + HEALTH_CHECK_SECONDS
        while time.time() < deadline:
            failed_urls = [u for u in HEALTH_URLS if not url_ok(u)]
            if not failed_urls:
                prune_result = prune_old_backups()
                return write_state(
                    download_in_progress=False,
                    update_in_progress=False,
                    update_phase="complete",
                    update_completed_at=now_ts(),
                    pending_restart=False,
                    reboot_requested=False,
                    post_reboot_pending=False,
                    post_reboot_waiting_for_restart=False,
                    rollback_required=False,
                    rollback_applied=False,
                    post_reboot_attempt=attempt,
                    post_reboot_checked_at=now_ts(),
                    last_successful_boot_version=installed_version(),
                    last_error=None,
                    **prune_result,
                )
            last_failed_urls = failed_urls
            time.sleep(HEALTH_POLL_SECONDS)

    reason = (
        f"Post-reboot health check failed after {HEALTH_CHECK_ATTEMPTS} attempts "
        f"of {HEALTH_CHECK_SECONDS} seconds. Failed URLs: {', '.join(last_failed_urls) or 'unknown'}"
    )
    result = restore_backup_after_failed_update(read_json(STATE_FILE, state), reason)

    if result.get("rollback_applied"):
        write_state(
            rollback_in_progress=True,
            rollback_reboot_requested=True,
            rollback_reboot_requested_at=now_ts(),
            rollback_reboot_requested_boot_id=system_boot_id(),
            update_in_progress=True,
            update_phase="awaiting_rollback_reboot",
            pending_restart=True,
            reboot_requested=True,
            last_error=f"{result.get('last_error')}; rebooting into restored version.",
        )
        proc = sudo_cmd("reboot", timeout=10)
        if proc.returncode != 0:
            return write_state(
                update_phase="awaiting_rollback_reboot",
                rollback_in_progress=True,
                rollback_reboot_requested=True,
                reboot_failed_at=now_ts(),
                last_error=f"{result.get('last_error')}; reboot after rollback failed: {proc.stderr.strip() or proc.stdout.strip()}",
            )
        return write_state(rollback_reboot_requested=True)

    return result


def post_rollback_check() -> dict[str, Any]:
    """Verify services after rebooting into a restored backup."""
    state = read_json(STATE_FILE, {})
    if not state.get("rollback_reboot_requested"):
        return write_state(post_rollback_checked_at=now_ts())

    if not boot_changed_since_update(state, rollback=True):
        return write_state(
            update_in_progress=True,
            update_phase="awaiting_rollback_reboot",
            pending_restart=True,
            rollback_in_progress=True,
            rollback_reboot_requested=True,
            post_rollback_pending=False,
        )

    last_failed_urls: list[str] = []
    for attempt in range(1, HEALTH_CHECK_ATTEMPTS + 1):
        write_state(
            update_in_progress=True,
            update_phase="verifying_rollback",
            rollback_in_progress=True,
            post_rollback_pending=True,
            rollback_post_reboot_attempt=attempt,
            rollback_post_reboot_attempts_total=HEALTH_CHECK_ATTEMPTS,
            post_rollback_checked_at=now_ts(),
            last_error=None if attempt == 1 else "Rollback verification is still waiting for services.",
        )

        deadline = time.time() + HEALTH_CHECK_SECONDS
        while time.time() < deadline:
            failed_urls = [u for u in HEALTH_URLS if not url_ok(u)]
            if not failed_urls:
                return write_state(
                    download_in_progress=False,
                    update_in_progress=False,
                    update_phase="complete",
                    update_completed_at=now_ts(),
                    pending_restart=False,
                    reboot_requested=False,
                    post_reboot_pending=False,
                    post_reboot_waiting_for_restart=False,
                    rollback_required=False,
                    rollback_in_progress=False,
                    rollback_reboot_requested=False,
                    post_rollback_pending=False,
                    rollback_post_reboot_attempt=None,
                    rollback_post_reboot_attempts_total=None,
                    rollback_verified_at=now_ts(),
                    rollback_verified_version=installed_version(),
                    last_successful_boot_version=installed_version(),
                    last_error=None,
                )
            last_failed_urls = failed_urls
            time.sleep(HEALTH_POLL_SECONDS)

    return write_state(
        download_in_progress=False,
        update_in_progress=False,
        update_phase="failed",
        update_failed_at=now_ts(),
        post_reboot_pending=False,
        post_reboot_waiting_for_restart=False,
        rollback_in_progress=False,
        rollback_reboot_requested=False,
        rollback_required=True,
        post_rollback_pending=False,
        rollback_post_reboot_attempt=None,
        rollback_post_reboot_attempts_total=None,
        post_rollback_checked_at=now_ts(),
        last_error=(
            "Rollback verification failed after "
            f"{HEALTH_CHECK_ATTEMPTS} attempts of {HEALTH_CHECK_SECONDS} seconds. "
            f"Failed URLs: {', '.join(last_failed_urls) or 'unknown'}"
        ),
    )

def install() -> dict[str, Any]:
    cfg = load_config()
    for path in [
        PROJECT_ROOT / "resources/userdata/Photos/full",
        PROJECT_ROOT / "resources/userdata/Photos/thumbs",
        PROJECT_ROOT / "resources/userdata/cache",
        PROJECT_ROOT / "resources/assets",
        RUNTIME_DIR,
    ]:
        path.mkdir(parents=True, exist_ok=True)
    if not CONFIG_FILE.exists():
        save_config(cfg)
    env_created = ensure_env_file()
    # reload after creating .env so diagnose/check can see values immediately if present
    load_dotenv()
    venv = PROJECT_ROOT / "venv"
    if not venv.exists():
        run([sys.executable, "-m", "venv", str(venv)], check=True, timeout=300)
    removed_special_files = cleanup_special_files(PROJECT_ROOT)
    fixed_permissions = repair_runtime_permissions()
    install_requirements()
    return replace_state(
        preserve_active_update=False,
        installed_version=installed_version(),
        installed_at=now_ts(),
        env_created=env_created,
        removed_special_files=removed_special_files,
        fixed_permissions=fixed_permissions,
        last_error=None,
    )


def diagnose() -> dict[str, Any]:
    cfg = load_config()
    updates = cfg.get("updates", {})
    repo = updates.get("repo", "")
    channel = updates.get("channel", "stable")
    url = (
        f"https://api.github.com/repos/{repo}/releases?per_page=10"
        if str(channel).startswith("pre")
        else f"https://api.github.com/repos/{repo}/releases/latest"
    )
    out: dict[str, Any] = {
        "updater_build": UPDATER_BUILD,
        "project_root": str(PROJECT_ROOT),
        "installed_version": installed_version(),
        "repo": repo,
        "channel": channel,
        "url": url,
        "github_token_loaded": bool(os.getenv("GITHUB_TOKEN", "").strip()),
        "env_exists": (PROJECT_ROOT / ".env").exists(),
        "service_files_exist": {
            "config_portal_service.py": (PROJECT_ROOT / "config_portal_service.py").exists(),
            "display_service.py": (PROJECT_ROOT / "display_service.py").exists(),
            "network_manager_service.py": (PROJECT_ROOT / "network_manager_service.py").exists(),
        },
        "services": DEFAULT_SERVICES,
        "required_systemd_units": REQUIRED_SYSTEMD_UNITS,
        "systemd": systemd_compatibility_state(),
        "backup_root": str(BACKUP_ROOT),
        "backup_retention_count": BACKUP_RETENTION_COUNT,
        "backup_count": len(list_backup_dirs()),
        "version_schema": "release.frontend.config.display.network.updater",
    }
    try:
        data = http_json(url)
        if isinstance(data, list):
            out["release_count"] = len(data)
            out["tags"] = [r.get("tag_name") for r in data]
        else:
            out["tag"] = data.get("tag_name")
    except Exception as exc:
        out["error"] = str(exc)
    return out


def print_json(data: dict[str, Any]) -> None:
    print(json.dumps(data, indent=2, sort_keys=True))


def main() -> int:
    parser = argparse.ArgumentParser(description="MementoFrame updater")
    parser.add_argument("command", choices=["install", "status", "check", "update", "reinstall", "autoupdate", "post-reboot-check", "post-rollback-check", "reboot", "diagnose", "repair-services", "prune-backups"])
    parser.add_argument("--no-reboot", action="store_true", help="Do not reboot after update/autoupdate")
    args = parser.parse_args()
    RUNTIME_DIR.mkdir(parents=True, exist_ok=True)
    operation_lock = None
    try:
        locked_commands = {
            "install", "check", "update", "reinstall", "autoupdate",
            "post-reboot-check", "post-rollback-check", "reboot",
            "repair-services", "prune-backups",
        }
        if args.command in locked_commands:
            operation_lock = interprocess_file_lock(
                UPDATER_LOCK_FILE,
                blocking=args.command != "autoupdate",
            )
            acquired = operation_lock.__enter__()
            if not acquired:
                state = read_json(STATE_FILE, {})
                state["auto_update_skipped"] = "updater_busy"
                print_json(state)
                return 0

        if args.command == "install":
            print_json(install())
        elif args.command == "status":
            state = read_json(STATE_FILE, {})
            state.setdefault("updater_build", UPDATER_BUILD)
            state.setdefault("installed_version", installed_version())
            print_json(state)
        elif args.command == "diagnose":
            print_json(diagnose())
        elif args.command == "repair-services":
            print_json(repair_systemd_services_if_needed())
        elif args.command == "prune-backups":
            print_json(prune_old_backups())
        elif args.command == "check":
            print_json(check_for_update())
        elif args.command == "update":
            result = apply_update()
            print_json(result)
            if result.get("applied_update") and not args.no_reboot:
                request_reboot()
        elif args.command == "reinstall":
            prepare_reinstall_current_release()
            result = apply_update(allow_reinstall=True)
            print_json(result)
            if result.get("applied_update") and not args.no_reboot:
                request_reboot()
        elif args.command == "autoupdate":
            print_json(autoupdate(no_reboot=args.no_reboot))
        elif args.command == "post-reboot-check":
            print_json(post_reboot_check())
        elif args.command == "post-rollback-check":
            print_json(post_rollback_check())
        elif args.command == "reboot":
            request_reboot()
            print_json(read_json(STATE_FILE, {}))
        return 0
    except Exception as exc:
        current_state = read_json(STATE_FILE, {})
        if active_update_state(current_state) and (
            current_state.get("pending_restart")
            or current_state.get("reboot_requested")
            or current_state.get("rollback_in_progress")
            or current_state.get("rollback_reboot_requested")
        ):
            write_state(last_error=str(exc))
        else:
            write_state(
                download_in_progress=False,
                update_in_progress=False,
                update_phase="failed",
                update_failed_at=now_ts(),
                last_error=str(exc),
            )
        print_json(read_json(STATE_FILE, {}))
        print(f"ERROR: {exc}", file=sys.stderr)
        return 1
    finally:
        if operation_lock is not None:
            operation_lock.__exit__(None, None, None)


if __name__ == "__main__":
    raise SystemExit(main())
