MrBroccoliJP/MementoFrame/mementoframe/network_manager_service.py

#!/usr/bin/env python3
# MementoFrame - Raspberry Pi Smart Photo Frame
# Copyright (c) 2026 João Fernandes
#
# This work is licensed under the Creative Commons Attribution-NonCommercial
# 4.0 International License. To view a copy of this license, visit:
# http://creativecommons.org/licenses/by-nc/4.0/

"""
ap_mode_manager.py

Brief:
    NetworkManager watchdog for switching the Raspberry Pi between normal Wi-Fi
    client mode and fallback Access Point mode.

Endpoints:
    None — this file does not expose HTTP routes or API endpoints.

Description:
    This service keeps the MementoFrame reachable even when the configured Wi-Fi
    network is unavailable. If no client Wi-Fi connection is active, it enables
    a local Access Point named ``MementoFrame``. While AP mode is active, it
    periodically checks saved Wi-Fi profiles and reconnects when possible.

Flow chart:

    ┌──────────────┐
    │ Start script │
    └──────┬───────┘
           │
           ▼
    ┌──────────────────────┐
    │ Check service conflicts│
    └──────┬───────────────┘
           │
           ▼
    ┌──────────────────────┐
    │ Ensure AP profile     │
    └──────┬───────────────┘
           │
           ▼
    ┌──────────────────────┐
    │ Patch client profiles │
    └──────┬───────────────┘
           │
           ▼
    ┌──────────────────────┐
    │ Watch network forever │
    └──────┬───────────────┘
           │
           ├── Wi-Fi connected ──► Monitor
           │
           └── No Wi-Fi ────────► Start AP mode
                                      │
                                      ▼
                              Periodically probe
                              saved Wi-Fi profiles
                                      │
                                      ▼
                              Reconnect or restore AP
"""

import json
import os
import subprocess
import sys
import time


# =============================================================================
# Configuration
# =============================================================================

# Wireless interface used by both client Wi-Fi and AP mode.
AP_INTERFACE = "wlan0"

# NetworkManager connection profile name for the fallback access point.
AP_CON_NAME = "MementoAP"

# Public SSID shown when the frame enters configuration mode.
AP_SSID = "MementoFrame"

# Gateway IP assigned to the Raspberry Pi while AP mode is active.
AP_IP = "192.168.4.1"

# Wi-Fi channel used by the access point profile.
AP_CHANNEL = "6"

# NetworkManager settings that define the fallback AP profile. These are applied
# on every startup so older or partially-created profiles get repaired in place.
AP_PROFILE_SETTINGS = [
    ("connection.autoconnect", "no"),
    ("connection.interface-name", AP_INTERFACE),
    ("802-11-wireless.ssid", AP_SSID),
    ("802-11-wireless.mode", "ap"),
    ("802-11-wireless.band", "bg"),
    ("802-11-wireless.channel", AP_CHANNEL),
    ("ipv4.method", "shared"),
    ("ipv4.addresses", f"{AP_IP}/24"),
    ("ipv6.method", "disabled"),
]

# Main watchdog loop interval.
CHECK_INTERVAL = 5

# Interval between saved-profile reconnect attempts while AP mode is active.
PROBE_EVERY = 120

# Maximum time to wait for each saved Wi-Fi profile to connect.
PROBE_TIMEOUT = 45

# Reconnect probes are delayed while a user is connected to AP/config portal.
AP_CLIENT_GRACE = 5 * 60

# Maximum AP uptime before forcing a reconnect probe, only when AP is idle.
MAX_AP_DURATION = 600

# Restart NetworkManager during AP-to-client transitions. This matches the
# manual recovery sequence that clears stuck supplicant/scan state on Pi Wi-Fi.
NETWORKMANAGER_SETTLE = 10
WIFI_RESCAN_SETTLE = 5

# Reboot once after a long Wi-Fi outage, then avoid reboot loops.
WIFI_REBOOT_AFTER = 60 * 60

# Shared runtime state used by the config portal and network watchdog.
RUNTIME_DIR = "runtime"
CONFIG_PORTAL_ACTIVITY_FILE = os.path.join(RUNTIME_DIR, "config_portal_activity.json")
WIFI_REBOOT_FLAG_FILE = os.path.join(RUNTIME_DIR, "rebooted_for_wifi_failure.flag")


# =============================================================================
# Runtime state
# =============================================================================

# Timestamp recorded when AP mode starts.
_ap_start_time = 0.0

# Timestamp recorded after the last reconnect probe.
_last_probe = 0.0

# Timestamp until which AP mode should not be interrupted because a client was
# recently seen. This covers drivers where station detection is intermittent.
_ap_client_hold_until = 0.0

# Timestamp recorded when Wi-Fi first became unavailable.
_wifi_down_since = 0.0

# Guard against the main loop fighting an in-progress reconnect attempt.
_reconnect_in_progress = False


# =============================================================================
# Shell helpers
# =============================================================================

def run(cmd, label=None):
    """
    Execute a shell command and return the CompletedProcess.

    This helper captures stdout/stderr so failures can be printed clearly while
    allowing the caller to decide whether the failure is fatal.
    """
    tag = label or " ".join(str(c) for c in cmd)
    proc = subprocess.run(cmd, capture_output=True, text=True)

    if proc.returncode != 0:
        print(f"  ❌ FAILED [{tag}]")
        if proc.stdout.strip():
            print(f"     stdout: {proc.stdout.strip()}")
        if proc.stderr.strip():
            print(f"     stderr: {proc.stderr.strip()}")

    return proc


def sh(cmd):
    """
    Execute a command and return stripped stdout.

    Raises:
        subprocess.CalledProcessError:
            Raised when the command exits with a non-zero status.
    """
    return subprocess.check_output(cmd, stderr=subprocess.DEVNULL).decode().strip()


def nmcli(*args):
    """
    Run an nmcli command with sudo.

    Args:
        *args:
            Arguments passed directly to ``nmcli``.
    """
    return run(["sudo", "nmcli"] + list(args))


# =============================================================================
# Runtime coordination helpers
# =============================================================================

def ensure_runtime_dir():
    """Ensure the shared runtime directory exists."""
    try:
        os.makedirs(RUNTIME_DIR, exist_ok=True)
    except Exception as e:
        print(f"  ⚠️ Could not create runtime directory: {e}")


def read_json_file(path):
    """Read a JSON file, returning None when it is missing or invalid."""
    try:
        with open(path, "r", encoding="utf-8") as f:
            return json.load(f)
    except FileNotFoundError:
        return None
    except Exception as e:
        print(f"  ⚠️ Could not read {path}: {e}")
        return None


def remove_file(path):
    """Remove a file if it exists."""
    try:
        os.remove(path)
    except FileNotFoundError:
        pass
    except Exception as e:
        print(f"  ⚠️ Could not remove {path}: {e}")


def clear_wifi_reboot_flag():
    """Allow a future one-shot Wi-Fi recovery reboot after Wi-Fi is healthy."""
    remove_file(WIFI_REBOOT_FLAG_FILE)


def create_wifi_reboot_flag():
    """Record that this outage already used its one-shot recovery reboot."""
    ensure_runtime_dir()
    try:
        with open(WIFI_REBOOT_FLAG_FILE, "w", encoding="utf-8") as f:
            f.write(str(time.time()))
    except Exception as e:
        print(f"  ⚠️ Could not write Wi-Fi reboot flag: {e}")


def wifi_reboot_flag_exists():
    """Return True when this outage already used its one-shot recovery reboot."""
    return os.path.exists(WIFI_REBOOT_FLAG_FILE)


def config_portal_quiet_until():
    """Return the timestamp until which AP mode should stay uninterrupted."""
    record = read_json_file(CONFIG_PORTAL_ACTIVITY_FILE)
    if not record:
        return 0.0

    try:
        return float(record.get("quiet_until") or 0.0)
    except (TypeError, ValueError):
        return 0.0


def config_portal_active():
    """Check whether the dashboard was loaded recently enough to hold AP mode."""
    return time.time() < config_portal_quiet_until()


def seconds_until_config_portal_idle():
    """Return remaining config portal quiet-window seconds."""
    return max(0, int(config_portal_quiet_until() - time.time()))


# =============================================================================
# Network state helpers
# =============================================================================

def current_connection():
    """
    Return the active NetworkManager connection name on the configured interface.

    Returns:
        str | None:
            The active connection name when wlan0 is connected, otherwise None.
    """
    try:
        out = sh(["nmcli", "-t", "-f", "DEVICE,TYPE,STATE,CONNECTION", "device", "status"])

        for line in out.splitlines():
            parts = line.split(":")

            if len(parts) >= 4 and parts[0] == AP_INTERFACE and parts[1] == "wifi":
                return parts[3] if parts[2] == "connected" else None

    except subprocess.CalledProcessError:
        pass

    return None


def ap_active():
    """
    Check whether the fallback access point profile is currently active.
    """
    return current_connection() == AP_CON_NAME


def wifi_connected():
    """
    Check whether the device is connected to a normal Wi-Fi client profile.
    """
    con = current_connection()
    return bool(con and con != AP_CON_NAME)


def clients_connected():
    """
    Check whether any client device is currently associated with the AP.

    Multiple signals are used because ``iw station dump`` can be empty on some
    drivers even while an SSH/config-portal client is active.
    """
    try:
        out = sh(["sudo", "iw", "dev", AP_INTERFACE, "station", "dump"])
        if "Station" in out:
            return True
    except subprocess.CalledProcessError:
        pass

    try:
        out = sh(["ss", "-H", "-tn", "state", "established"])
        if "192.168.4." in out:
            return True
    except subprocess.CalledProcessError:
        pass

    try:
        out = sh(["ip", "neigh", "show", "dev", AP_INTERFACE])
        for line in out.splitlines():
            if "192.168.4." in line and "FAILED" not in line:
                return True
    except subprocess.CalledProcessError:
        pass

    return False


def ap_should_hold():
    """
    Return a reason to keep AP mode stable, or None when probing is allowed.

    AP mode is protected when a client is connected, when a client was recently
    seen, or when the config dashboard was loaded recently.
    """
    global _ap_client_hold_until

    now = time.time()

    if clients_connected():
        _ap_client_hold_until = max(_ap_client_hold_until, now + AP_CLIENT_GRACE)
        return f"AP client active — delaying reconnect for {AP_CLIENT_GRACE // 60} minutes."

    if now < _ap_client_hold_until:
        remaining = int(_ap_client_hold_until - now)
        return f"AP client was recently active — delaying reconnect for {remaining}s."

    if config_portal_active():
        remaining = seconds_until_config_portal_idle()
        return f"Config portal active — delaying reconnect for {remaining}s."

    return None


# =============================================================================
# First-run setup
# =============================================================================

def check_for_conflicts():
    """
    Stop startup if services that conflict with NetworkManager AP mode are active.

    NetworkManager uses its own internal dnsmasq behavior for shared connections.
    Running hostapd or dnsmasq separately can prevent AP mode from working
    reliably.
    """
    conflicts = []

    for service in ["hostapd", "dnsmasq"]:
        try:
            if sh(["systemctl", "is-active", service]) == "active":
                conflicts.append(service)

        except subprocess.CalledProcessError:
            pass

    if conflicts:
        print("❌ Conflicting services are running:")
        for s in conflicts:
            print(f"   - {s}")

        print("\nNetworkManager AP mode uses internal dnsmasq. Disable conflicts:")
        for s in conflicts:
            print(f"   sudo systemctl stop {s} && sudo systemctl disable {s}")

        sys.exit(1)


def ap_profile_exists():
    """
    Check whether the fallback AP NetworkManager profile already exists.
    """
    try:
        out = sh(["nmcli", "-t", "-f", "NAME", "connection", "show"])
        return AP_CON_NAME in out.splitlines()

    except subprocess.CalledProcessError:
        return False


def ensure_ap_profile():
    """
    Create the NetworkManager AP profile when it does not already exist.

    The profile is configured as:
        - Wi-Fi access point mode
        - IPv4 shared networking
        - Static gateway address
        - IPv6 disabled
        - Wi-Fi power saving disabled where possible
    """
    exists = ap_profile_exists()

    if exists:
        print(f"🔧 Repairing NetworkManager AP profile '{AP_CON_NAME}'…")
    else:
        print(f"🔧 Creating NetworkManager AP profile '{AP_CON_NAME}'…")

        run(
            ["sudo", "nmcli", "connection", "delete", AP_CON_NAME],
            label=f"cleanup stale {AP_CON_NAME}",
        )

        if run(
            [
                "sudo", "nmcli", "connection", "add",
                "type", "wifi", "ifname", AP_INTERFACE,
                "con-name", AP_CON_NAME, "autoconnect", "no", "ssid", AP_SSID,
            ],
            label=f"create {AP_CON_NAME}",
        ).returncode != 0:
            print("❌ AP profile creation failed.")
            sys.exit(1)

    for key, value in AP_PROFILE_SETTINGS:
        if run(
            [
                "sudo", "nmcli", "connection", "modify", AP_CON_NAME,
                key, value,
            ],
            label=f"set {AP_CON_NAME} {key}",
        ).returncode != 0:
            print("❌ AP profile configuration failed.")
            sys.exit(1)

    conn_file = f"/etc/NetworkManager/system-connections/{AP_CON_NAME}.nmconnection"

    try:
        with open(conn_file, "r", encoding="utf-8") as f:
            content = f.read()

        if "powersave=" not in content:
            content = content.replace("[wifi]\n", "[wifi]\npowersave=2\n")

            with open(conn_file, "w", encoding="utf-8") as f:
                f.write(content)

        run(["sudo", "nmcli", "connection", "reload"])

    except (FileNotFoundError, PermissionError) as e:
        print(f"  ⚠️ Could not write powersave setting: {e}")

    print(f"  ✅ AP profile ready — SSID: {AP_SSID} | Gateway: {AP_IP}")


def ensure_client_profiles_patched():
    """
    Enable autoconnect on all saved Wi-Fi client profiles.

    The AP profile itself is excluded so NetworkManager does not automatically
    start the fallback AP unless this watchdog explicitly requests it.
    """
    try:
        profiles_out = sh(["nmcli", "-t", "-f", "NAME,TYPE", "connection", "show"])

    except subprocess.CalledProcessError:
        return

    for line in profiles_out.splitlines():
        parts = line.split(":", 1)

        if len(parts) != 2 or parts[1] != "802-11-wireless":
            continue

        name = parts[0]

        if name == AP_CON_NAME:
            continue

        run(
            [
                "sudo", "nmcli", "connection", "modify", name,
                "connection.autoconnect", "yes",
                "connection.autoconnect-retries", "0",
            ],
            label=f"patch client profile {name}",
        )


# =============================================================================
# Mode switching
# =============================================================================

def prepare_wifi_device_for_ap():
    """
    Put the Wi-Fi device in a clean state before activating AP mode.

    NetworkManager can leave wlan0 disconnected, unmanaged, or radio-disabled
    after failed client connection attempts. These commands are intentionally
    best-effort; AP activation still reports the real failure if it cannot start.
    """
    run(["sudo", "nmcli", "radio", "wifi", "on"], label="wifi radio on before AP")
    run(
        ["sudo", "nmcli", "device", "set", AP_INTERFACE, "managed", "yes"],
        label=f"ensure {AP_INTERFACE} managed",
    )
    run(
        ["sudo", "nmcli", "device", "disconnect", AP_INTERFACE],
        label=f"clear {AP_INTERFACE} state before AP",
    )
    time.sleep(2)


def start_ap():
    """
    Activate fallback AP mode.

    Returns:
        bool:
            True when AP mode is already active or successfully started.
    """
    global _ap_start_time

    if ap_active():
        return True

    print("📡 Activating AP mode…")

    prepare_wifi_device_for_ap()
    result = nmcli("connection", "up", AP_CON_NAME)

    if result.returncode != 0:
        print("  ⚠️ AP activation failed once; retrying after NetworkManager reload.")
        run(["sudo", "nmcli", "connection", "reload"], label="reload NetworkManager connections")
        prepare_wifi_device_for_ap()
        result = nmcli("connection", "up", AP_CON_NAME)

    if result.returncode != 0:
        print("  ❌ AP activation failed.")
        return False

    time.sleep(3)

    _ap_start_time = time.time()

    print(f"  ✅ AP '{AP_SSID}' live at {AP_IP}")
    return True


def stop_ap():
    """
    Deactivate fallback AP mode.

    Returns:
        bool:
            True when AP mode is inactive or successfully stopped.
    """
    if not ap_active():
        return True

    print("🔌 Deactivating AP mode…")

    result = nmcli("connection", "down", AP_CON_NAME)

    if result.returncode != 0:
        run(
            ["sudo", "nmcli", "device", "disconnect", AP_INTERFACE],
            label="device disconnect fallback",
        )
        return False

    time.sleep(2)

    print("  AP stopped. NetworkManager can connect client profiles now.")
    return True



def reset_networkmanager_for_client_mode():
    """Reset NetworkManager before trying client Wi-Fi from AP mode."""
    print("♻️ Resetting NetworkManager before Wi-Fi reconnect…")

    stop_ap()

    run(
        ["sudo", "nmcli", "device", "disconnect", AP_INTERFACE],
        label="disconnect wlan0 before NetworkManager reset",
    )

    result = run(
        ["sudo", "systemctl", "restart", "NetworkManager"],
        label="restart NetworkManager",
    )

    if result.returncode != 0:
        print("  ⚠️ NetworkManager restart failed; continuing with nmcli reset only.")

    time.sleep(NETWORKMANAGER_SETTLE)

    run(["sudo", "nmcli", "radio", "wifi", "on"], label="wifi radio on")
    time.sleep(2)

    run(
        ["sudo", "nmcli", "device", "wifi", "rescan", "ifname", AP_INTERFACE],
        label="wifi rescan",
    )
    time.sleep(WIFI_RESCAN_SETTLE)


# =============================================================================
# Reconnect probing
# =============================================================================

def known_client_profiles():
    """
    Return saved Wi-Fi client profile names, excluding the AP profile.
    """
    profiles = []

    try:
        out = sh(["nmcli", "-t", "-f", "NAME,TYPE", "connection", "show"])

    except subprocess.CalledProcessError:
        return profiles

    for line in out.splitlines():
        parts = line.split(":", 1)

        if len(parts) == 2 and parts[1] == "802-11-wireless" and parts[0] != AP_CON_NAME:
            profiles.append(parts[0])

    return profiles


def probe_reconnect(force=False):
    """
    Try reconnecting to saved Wi-Fi client profiles.

    The AP-to-client transition intentionally restarts NetworkManager because
    Raspberry Pi Wi-Fi can get stuck after AP mode. If every profile fails, AP
    mode is restored so the frame stays reachable.
    """
    global _reconnect_in_progress

    if _reconnect_in_progress:
        print("🔁 Reconnect already in progress — skipping duplicate probe.")
        return False

    if ap_active() and not force:
        hold_reason = ap_should_hold()
        if hold_reason:
            print(f"🛠 {hold_reason}")
            return False

    print("🔎 Probing saved Wi-Fi profiles…")

    profiles = known_client_profiles()

    if not profiles:
        print("  No saved Wi-Fi profiles — staying in AP mode.")
        return False

    _reconnect_in_progress = True

    try:
        reset_networkmanager_for_client_mode()

        for profile in profiles:
            print(f"  Trying saved profile: {profile}")

            run(
                [
                    "sudo", "nmcli", "connection", "modify", profile,
                    "802-11-wireless-security.wps-method", "disabled",
                ],
                label=f"disable WPS for {profile}",
            )

            nmcli("connection", "up", profile)

            deadline = time.time() + PROBE_TIMEOUT

            while time.time() < deadline:
                if wifi_connected():
                    print(f"  ✅ Reconnected to Wi-Fi: {profile}")
                    clear_wifi_reboot_flag()
                    return True

                time.sleep(2)

        print("  ⏳ All saved profiles failed — restoring AP.")
        start_ap()
        return False

    finally:
        _reconnect_in_progress = False


# =============================================================================
# Main watchdog loop
# =============================================================================

def main():
    """
    Initialize NetworkManager configuration and continuously monitor connectivity.
    """
    global _last_probe, _wifi_down_since

    ensure_runtime_dir()
    check_for_conflicts()
    ensure_ap_profile()
    ensure_client_profiles_patched()

    print()
    print("🖼  MementoFrame AP Mode Manager")
    print(f"   Interface : {AP_INTERFACE}")
    print(f"   AP SSID   : {AP_SSID} (open network — config portal PIN protects dashboard)")
    print(f"   Gateway   : {AP_IP}")
    print()

    while True:
        now = time.time()

        if wifi_connected():
            if _wifi_down_since:
                print("📶 Wi-Fi restored — clearing recovery state.")
            else:
                print("📶 Connected to Wi-Fi — monitoring…")

            _wifi_down_since = 0.0
            clear_wifi_reboot_flag()

        else:
            if not _wifi_down_since:
                _wifi_down_since = now

            if not ap_active():
                if config_portal_active() or _reconnect_in_progress:
                    print("🛠 Wi-Fi transition/config portal active — not restoring AP yet.")
                else:
                    print("⚠️ No Wi-Fi — entering AP mode.")
                    start_ap()
                    _last_probe = now

            else:
                hold_reason = ap_should_hold()

                if hold_reason:
                    print(f"🛠 {hold_reason}")
                    _last_probe = now

                else:
                    uptime = now - _ap_start_time if _ap_start_time else 0
                    since_probe = now - _last_probe

                    if uptime > MAX_AP_DURATION:
                        print(f"⏰ AP up {uptime:.0f}s and idle — forcing reconnect probe.")
                        probe_reconnect(force=True)
                        _last_probe = now

                    elif since_probe >= PROBE_EVERY:
                        probe_reconnect(force=False)
                        _last_probe = now

                    if (
                        _wifi_down_since
                        and now - _wifi_down_since >= WIFI_REBOOT_AFTER
                        and not wifi_reboot_flag_exists()
                    ):
                        print("🔁 Wi-Fi has been down for over 1 hour — rebooting once for recovery.")
                        create_wifi_reboot_flag()
                        run(["sudo", "reboot"], label="wifi recovery reboot")

        time.sleep(CHECK_INTERVAL)


if __name__ == "__main__":
    main()
